the-chenergy/grid88_qmk_firmware/gallery/2.jpg

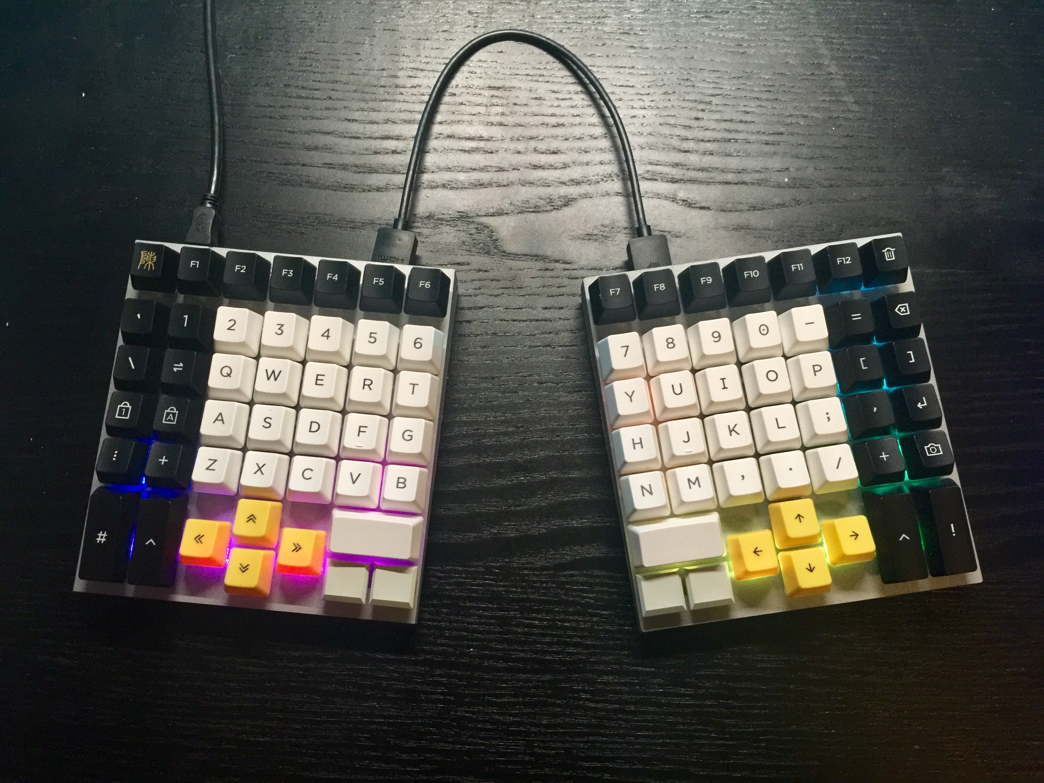
gallery/2.jpg
